AnandKapadia/iCycle-WSN/02_Software/02_03_Master/data/bicycle.bmp

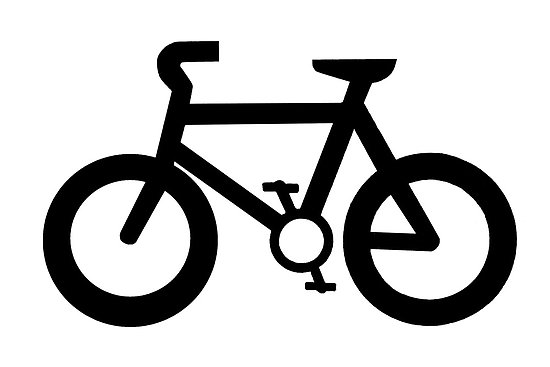
02_Software/02_03_Master/data/bicycle.bmp
