AnandKapadia/iCycle-WSN/02_Software/02_03_Master/data/vehicle.bmp

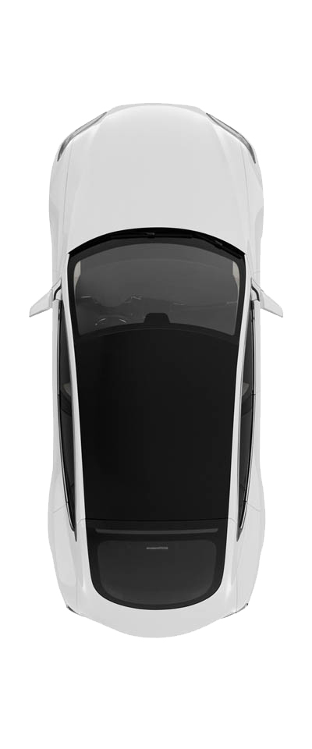
02_Software/02_03_Master/data/vehicle.bmp
