AnandKapadia/iCycle-WSN/02_Software/02_02_Arduino/AtCommand/AtCommand.ino

/**
 * Copyright (c) 2009 Andrew Rapp. All rights reserved.
 *
 * This file is part of XBee-Arduino.
 *
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
 * You should have received a copy of the GNU General Public License
 * along with XBee-Arduino.  If not, see <http://www.gnu.org/licenses/>.
 */

#include <XBee.h>
#include <SoftwareSerial.h>

/*
This example is for Series 1 (10C8 or later firmware) or Series 2 XBee radios
Sends a few AT command queries to the radio and checks the status response for success

This example uses the SoftSerial library to view the XBee communication.  I am using a 
Modern Device USB BUB board (http://moderndevice.com/connect) and viewing the output
with the Arduino Serial Monitor.
*/


XBee xbee = XBee();

// rssi
uint8_t dbCmd[] = {'D','B'};

AtCommandRequest atRequest = AtCommandRequest(dbCmd);

AtCommandResponse atResponse = AtCommandResponse();

void setup() { 
  Serial.begin(9600);
  xbee.begin(Serial);
  // start soft serial
  Serial.begin(9600);
  
  // Startup delay to wait for XBee radio to initialize.
  // you may need to increase this value if you are not getting a response
  delay(5000);
}

void loop() {

  // get SH
  sendAtCommand();
  
  // we're done.  Hit the Arduino reset button to start the sketch over
  while (1) {};
}

void sendAtCommand() {
  Serial.println("Sending command to the XBee");

  // send the command
  xbee.send(atRequest);

  // wait up to 5 seconds for the status response
  if (xbee.readPacket(5000)) {
    // got a response!

    // should be an AT command response
    if (xbee.getResponse().getApiId() == AT_COMMAND_RESPONSE) {
      xbee.getResponse().getAtCommandResponse(atResponse);

      if (atResponse.isOk()) {
        Serial.print("Command [");
        Serial.print(atResponse.getCommand()[0]);
        Serial.print(atResponse.getCommand()[1]);
        Serial.println("] was successful!");

        if (atResponse.getValueLength() > 0) {
          Serial.print("Command value length is ");
          Serial.println(atResponse.getValueLength(), DEC);

          Serial.print("Command value: ");
          
          for (int i = 0; i < atResponse.getValueLength(); i++) {
            Serial.print(atResponse.getValue()[i], HEX);
            Serial.print(" ");
          }

          Serial.println("");
        }
      } 
      else {
        Serial.print("Command return error code: ");
        Serial.println(atResponse.getStatus(), HEX);
      }
    } else {
      Serial.print("Expected AT response but got ");
      Serial.print(xbee.getResponse().getApiId(), HEX);
    }   
  } else {
    // at command failed
    if (xbee.getResponse().isError()) {
      Serial.print("Error reading packet.  Error code: ");  
      Serial.println(xbee.getResponse().getErrorCode());
    } 
    else {
      Serial.print("No response from radio");  
    }
  }
}
