AnandKapadia/iCycle-WSN/02_Software/02_03_AtmelMole/BikeMole/BikeMole/src/config/config.h

/**
 * \file config.h
 *
 * \brief WSNDemo application and stack configuration
 *
 * Copyright (C) 2014-2015 Atmel Corporation. All rights reserved.
 *
 * \asf_license_start
 *
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
 * 3. The name of Atmel may not be used to endorse or promote products derived
 *    from this software without specific prior written permission.
 *
 * 4. This software may only be redistributed and used in connection with an
 *    Atmel microcontroller product.
 *
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
 * \asf_license_stop
 *
 *
 */

/*
 * Copyright (c) 2014-2015 Atmel Corporation. All rights reserved.
 *
 * Licensed under Atmel's Limited License Agreement --> EULA.txt
 */
#ifndef _CONFIG_H_
#define _CONFIG_H_

// Timer Periods/Intervals
#define RX_RESPONSE_HOLD_MS     500
#define TX_BIKE_PACKET_MS       250

// IO Mapping
#define TX_LED ((IOPORT_PORTB << 3) | 0x06)
#define RX_LED ((IOPORT_PORTB << 3) | 0x07)
#define LEFT_LED ((IOPORT_PORTG << 3) | 0x01)
#define RIGHT_LED ((IOPORT_PORTG << 3) | 0x02)
//#define BUZZER_PIN
    
/*****************************************************************************
*****************************************************************************/
#define APP_ADDR                0x4242
#define APP_PANID               0x1239
#define APP_SENDING_INTERVAL    10000
#define APP_ENDPOINT            1
#define APP_SECURITY_KEY        "TestSecurityKey0"

#if (defined (PHY_AT86RF212B) || defined (PHY_AT86RF212))
  #define APP_CHANNEL           0x0F
  #define APP_BAND              0x00
  #define APP_MODULATION        0x24
#else
  #define APP_CHANNEL           0x0F
#endif

/* #define PHY_ENABLE_RANDOM_NUMBER_GENERATOR */

//#define SYS_SECURITY_MODE                   0

#define NWK_BUFFERS_AMOUNT                  10
#define NWK_DUPLICATE_REJECTION_TABLE_SIZE  50
#define NWK_DUPLICATE_REJECTION_TTL         2000 /* ms */
#define NWK_ROUTE_TABLE_SIZE                100
#define NWK_ROUTE_DEFAULT_SCORE             3
#define NWK_ACK_WAIT_TIME                   1000 /* ms */
#define NWK_GROUPS_AMOUNT                   3
#define NWK_ROUTE_DISCOVERY_TABLE_SIZE      6
#define NWK_ROUTE_DISCOVERY_TIMEOUT         1000 /* ms */
#define APP_RX_BUF_SIZE                     5
//#define NWK_ENABLE_ROUTING
//#define NWK_ENABLE_SECURITY
//#define NWK_ENABLE_ROUTE_DISCOVERY

/*
#if APP_ADDR == 0
#define APP_CAPTION     "Coordinator"
#define APP_NODE_TYPE   0
#define APP_COORDINATOR 1
#define APP_ROUTER      0
#define APP_ENDDEVICE   0
#elif APP_ADDR < 0x8000
#define APP_CAPTION     "Router"
#define APP_NODE_TYPE   1
#define APP_COORDINATOR 0
#define APP_ROUTER      1
#define APP_ENDDEVICE   0
#else
#define APP_CAPTION     "End Device"
#define APP_NODE_TYPE   2
#define APP_COORDINATOR 0
#define APP_ROUTER      0
#define APP_ENDDEVICE   1
#endif
*/
#endif /* _CONFIG_H_ */
